ANDnXOR/ANDnXOR_DC26_Badge/Firmware/components/console_gfx.c

/*****************************************************************************
 * Made with beer and late nights in California.
 *
 * (C) Copyright 2017-2018 AND!XOR LLC (http://andnxor.com/).
 *
 * PROPRIETARY AND CONFIDENTIAL UNTIL AUGUST 7th, 2018 then,
 *
 * Licensed under the Apache License, Version 2.0 (the "License");
 * you may not use this file except in compliance with the License.
 * You may obtain a copy of the License at
 *
 *     http://www.apache.org/licenses/LICENSE-2.0
 *
 * Unless required by applicable law or agreed to in writing, software
 * distributed under the License is distributed on an "AS IS" BASIS,
 * WITHOUT WARRANTIES OR CONDITIONS OF ANY KIND, either express or implied.
 * See the License for the specific language governing permissions and
 * limitations under the License.
 *
 * ADDITIONALLY:
 * If you find this source code useful in anyway, use it in another electronic
 * conference badge, or just think it's neat. Consider buying us a beer
 * (or two) and/or a badge (or two). We are just as obsessed with collecting
 * badges as we are in making them.
 *
 * Contributors:
 *   @andnxor
 *   @zappbrandnxor
 *   @hyr0n1
 *   @exc3ls1or
 *   @lacosteaef
 *   @bitstr3m
 *****************************************************************************/

#include "system.h"

void console_gfx_area_banner(int i){
    switch(i){
		case 0 : util_print_nice(
				"\n"
				"           ██░ ██  ▒█████   ███▄ ▄███▓▓█████     ██▒   █▓ ██▓ ██▓     ██▓    ▄▄▄        ▄████ ▓█████ \n"
				"          ▓██░ ██▒▒██▒  ██▒▓██▒▀█▀ ██▒▓█   ▀    ▓██░   █▒▓██▒▓██▒    ▓██▒   ▒████▄     ██▒ ▀█▒▓█   ▀ \n"
				"          ▒██▀▀██░▒██░  ██▒▓██    ▓██░▒███       ▓██  █▒░▒██▒▒██░    ▒██░   ▒██  ▀█▄  ▒██░▄▄▄░▒███   \n"
				"          ░▓█ ░██ ▒██   ██░▒██    ▒██ ▒▓█  ▄      ▒██ █░░░██░▒██░    ▒██░   ░██▄▄▄▄██ ░▓█  ██▓▒▓█  ▄ \n"
				"          ░▓█▒░██▓░ ████▓▒░▒██▒   ░██▒░▒████▒      ▒▀█░  ░██░░██████▒░██████▒▓█   ▓██▒░▒▓███▀▒░▒████▒\n"
				"           ▒ ░░▒░▒░ ▒░▒░▒░ ░ ▒░   ░  ░░░ ▒░ ░      ░ ▐░  ░▓  ░ ▒░▓  ░░ ▒░▓  ░▒▒   ▓▒█░ ░▒   ▒ ░░ ▒░ ░\n"
				"           ▒ ░▒░ ░  ░ ▒ ▒░ ░  ░      ░ ░ ░  ░      ░ ░░   ▒ ░░ ░ ▒  ░░ ░ ▒  ░ ▒   ▒▒ ░  ░   ░  ░ ░  ░\n"
				"           ░  ░░ ░░ ░ ░ ▒  ░      ░      ░           ░░   ▒ ░  ░ ░     ░ ░    ░   ▒   ░ ░   ░    ░   \n"
				"           ░  ░  ░    ░ ░         ░      ░  ░         ░   ░      ░  ░    ░  ░     ░  ░      ░    ░  ░\n"
				"                                                     ░                                               \n"
				"\n"
				"                 ╡░                                                                             ╡░    \n"
				"                 ╡░        ╡░                                                        ╡░         ╡░    \n"
				"               ╡░╡░╡░      ╡░         ╡░                                  ╡░         ╡░       ╡░╡░╡░  \n"
				"               ╡░░░░░    ╡░╡░╡░       ╡░                                  ╡░       ╡░╡░╡░     ╡░░░░░  \n"
				"                 ╡░      ╡░░░░░     ╡░╡░╡░          ≈≈≈≈≈≈≈≈≈≈≈≈≈≈≈≈≈   ╡░╡░╡░     ╡░░░░░       ╡░    \n"
				"         ·*··∙.  ╡░        ╡░       ╡░░░░░         ≈≈≈≈≈≈≈≈≈≈≈≈≈≈≈≈≈    ╡░░░░░       ╡░         ╡░    \n"
				"         ······°·····∙·    ╡░         ╡░          ≈≈≈≈≈≈≈≈≈≈≈≈≈≈≈≈≈║      ╡░         ╡░     ··.·······\n"
				"         ▓▓▓▓▓·∙.··∙·.·········∙·     ╡░         ≈≈≈≈≈≈≈≈≈≈≈≈≈≈≈≈≈ ║      ╡░   ··°·.·∙····∙··▓▓▓▓▓▓▓▓▓\n"
				"         ▓▓▓▓▓▓▓▓▓▓▓▓▓··.·*···········╡░·····   ≈≈≈≈≈≈≈≈≈≈≈≈≈≈≈≈≈  ║  ····╡░*.···▓▓▓▓▓▓▓▓▓▓▓▓▓▓▓▓▓▓▓▓▓\n"
				"         ··▓▓▓▓▓▓▓▓▓▓▓▓▓▓▓▓▓▓▓▓▓▓▓·∙····*···∙····║·  ║         ║   ║·.··∙·······▓▓▓▓▓▓▓▓▓▓▓▓▓▓▓·······\n"
				"         ···········▓▓▓▓▓▓▓▓▓▓▓▓▓▓▓▓▓▓▓▓▓▓▓▓···∙·║···║·┌┐···.··║···║···▓▓▓▓▓▓▓▓▓▓▓▓▓▓▓···········∙··*·\n"
				"         ···°.···*···········▓▓▓▓▓▓▓▓▓▓▓▓▓▓▓▓▓▓▓▓║▓··║·││··◙···║·.·║▓▓▓▓▓▓▓▓▓▓▓▓▓▓▓▓▓▓····╡░··°·······\n"
				"         ·*··.∙°········∙∙∙·········.····▓▓▓▓▓▓▓▓║▓▓▓║▓││┌───┐▓║▓▓▓║▓▓▓▓▓▓·········∙······╡░····*·····\n"
				"         ··∙······.··╡░······∙∙·····∙··········▓▓║▓▓▓▓▓╘╛▓▓▓▓▓▓║▓▓▓▓▓······*···╡░···°···╡░╡░╡░·····.°·\n"
				"         ······∙·····╡░···*··.···╡░··.°·*·······▓║▓▓▓▓▓▓▓▓▓▓▓▓▓║▓▓····.∙·······╡░·······╡░░░░░····°···\n"
				"         ·∙··*···.·╡░╡░╡░···∙····╡░········.····▓║▓░δ▓▓▓▓▓▓▓▓▓▓║▓···°····.···╡░╡░╡░··*∙···╡░···.····∙·\n"
				"         ··········╡░░░░░······╡░╡░╡░···∙······▓▓║▓░░▓▓▓▓▓▓▓▓▓▓║▓▓···∙···∙···╡░░░░░·······╡░·∙···╡░···\n"
				"         °··╡░···°···╡░······*·╡░░░░░·········▓▓▓▓▓▓▓▓▓▓▓▓▓▓▓▓▓▓▓▓▓···*········╡░···°··∙··╡░·····╡░···\n"
				"         ·.·╡░··.····╡░·.·∙.·····╡░····∙°··▓▓▓▓▓▓··········∙····▓▓▓▓▓▓··°.··*··╡░·∙··.·∙·······╡░╡░╡░·\n"
				"         ·╡░╡░╡░·····╡░·····∙····╡░······▓▓▓▓▓▓▓·∙·τ·········∙···▓▓▓▓▓▓▓·······╡░···∙···*····.·╡░░░░░·\n"
				"         ·╡░░░░░··∙*·············╡░··▓▓▓▓▓▓▓▓▓·····☺≡≡≡⌐··..*······▓▓▓▓▓▓▓▓▓▓········°···········╡░···\n"
				"         ···╡░········∙·.····▓▓▓▓▓▓▓▓▓▓▓▓▓·····∙····╘·╘·······.·∙·······▓▓▓▓▓▓▓▓▓▓▓▓·············╡░···\n"
				"         ···╡░······°·····▓▓▓▓▓▓▓▓▓▓▓·°···∙······∙·······°······.·······.··▓▓▓▓▓▓▓▓▓▓▓▓··∙°··*···╡░···\n"
				"         ···╡░··▓▓▓▓▓▓▓▓▓▓▓▓▓·····∙···∙···∙··*···°·····∙·.··..··.··°··············▓▓▓▓▓▓▓▓▓▓▓▓▓·······\n"
				"         ▓▓▓▓▓▓▓▓▓▓▓▓▓▓▓▓▓·····°····*············∙····°·········.···*······..········▓▓▓▓▓▓▓▓▓▓▓▓▓▓▓▓▓\n"
				"\n");
				break;

    	case 1 : util_print_nice(
    			"\n"
    			"     ███▄    █  ▒█████   ██▀███  ▄▄▄█████▓ ██░ ██     ██▒   █▓ ██▓ ██▓     ██▓    ▄▄▄        ▄████ ▓█████ \n"
    			"     ██ ▀█   █ ▒██▒  ██▒▓██ ▒ ██▒▓  ██▒ ▓▒▓██░ ██▒   ▓██░   █▒▓██▒▓██▒    ▓██▒   ▒████▄     ██▒ ▀█▒▓█   ▀ \n"
    			"    ▓██  ▀█ ██▒▒██░  ██▒▓██ ░▄█ ▒▒ ▓██░ ▒░▒██▀▀██░    ▓██  █▒░▒██▒▒██░    ▒██░   ▒██  ▀█▄  ▒██░▄▄▄░▒███   \n"
    			"    ▓██▒  ▐▌██▒▒██   ██░▒██▀▀█▄  ░ ▓██▓ ░ ░▓█ ░██      ▒██ █░░░██░▒██░    ▒██░   ░██▄▄▄▄██ ░▓█  ██▓▒▓█  ▄ \n"
    			"    ▒██░   ▓██░░ ████▓▒░░██▓ ▒██▒  ▒██▒ ░ ░▓█▒░██▓      ▒▀█░  ░██░░██████▒░██████▒▓█   ▓██▒░▒▓███▀▒░▒████▒\n"
    			"    ░ ▒░   ▒ ▒ ░ ▒░▒░▒░ ░ ▒▓ ░▒▓░  ▒ ░░    ▒ ░░▒░▒      ░ ▐░  ░▓  ░ ▒░▓  ░░ ▒░▓  ░▒▒   ▓▒█░ ░▒   ▒ ░░ ▒░ ░\n"
    			"    ░ ░░   ░ ▒░  ░ ▒ ▒░   ░▒ ░ ▒░    ░     ▒ ░▒░ ░      ░ ░░   ▒ ░░ ░ ▒  ░░ ░ ▒  ░ ▒   ▒▒ ░  ░   ░  ░ ░  ░\n"
    			"       ░   ░ ░ ░ ░ ░ ▒    ░░   ░   ░       ░  ░░ ░        ░░   ▒ ░  ░ ░     ░ ░    ░   ▒   ░ ░   ░    ░   \n"
    			"             ░     ░ ░     ░               ░  ░  ░         ░   ░      ░  ░    ░  ░     ░  ░      ░    ░  ░\n"
    			"                                                          ░                                               \n"
				"\n"
				"     ▲▲▲▲▲▲▲▲▲▲▲▲▲▲▲▲▲▲▲▲▲▲▲▲▲▲▲▲▲▲▲▲▲▲▲▲▲▲▲▲▲▲▲▲▲▲▲▲▲▲▲▲▲▲▲▲▲▲▲▲▲▲▲▲▲▲▲▲▲▲▲▲▲▲▲▲▲▲▲▲▲▲▲▲▲▲▲▲▲▲▲▲▲▲▲▲▲▲▲▲\n"
    			"     ════════════════════════════════════════════════════════════════════════════════════════════════════\n"
				"     ████████████████████████████████████████████████████████████████████████████████████████████████████\n"
				"     ░░░░░░░░░░░░░░░░░░░░░░░░░░░░░░░░░░░░░░░░░░░░░░░░░░░░░░░░░░░░░░░░░░░░░░░░░░░░░░░░░░░░░░░░░░░░░░░░░░░░\n"
				"     ░░░░░░░░░░░░░░░░░░░░░░░░░░░░░░░░░░░░░░░░░░░░░░░░░░░░░░░░░░░░░░░░░░░░░░░░░░░░░░░░░░░░░░░░░░░░░░░░░░░░\n"
				"     ░░░░░░░░░░░░░░░░░░░░░░░░░░░░░░░░░░░░░░░░░░░░░░░░░░░░░░░░░░░░░░░░░░░░░░░░░░░░░░░░░░░░░░░░░░░░░░░░░░░░\n"
				"     ░░░░░░░░░▒▒▒▒▒░░░░░░░░░░░░░░░░░░░░░░░░░░░░░░░░░░░░░░░░░░░░░░░░░┌─────────────┐░░░░░░░░░░░░░░░░░░░░░░\n"
				"     ░░░░░░░░▒     ▒░░░░░░░░░░░░░░░░░░░░░░░░░░░╔═══════╦═══════╗░░░░│ COMDEX TIX! │░░░░░░«≈≈≈≈≈≈≈≈≈»░░░░░\n"
				"     ░░░░░░░▒       ▒░░░░░░░┌─────────────┐░░░░║       ║       ║░░░░│             │░░░░░░« WANTED! »░░░░░\n"
				"     ░░░░░░▒ ░░░░    ▒░░░░░░││Lead Solder││░░░░║       ║       ║░░░░│PREORDER NOW!│░░░░░░«    •    »░░░░░\n"
				"     ░░░░░▒  ░   ░    ▒░░░░░││ Only 0.25 ││░░░░║       ║       ║░░░░│             │░░░░░░«    │    »░░░░░\n"
				"     ░░░░░▒  ░   ░    ▒░░░░░│             │░░░░║       ║       ║░░░░│ COMES  WITH │░░░░░░«   ░░░   »░░░░░\n"
				"     ░░░░░▒  ░░░░     ▒░░░░░│TRS-80 POCKET│░░░░║       ║       ║░░░░│  CARDSTOCK  │░░░░░░«  (○░○)  »░░░░░\n"
				"     ░░░░░▒  ░  ░     ▒░░░░░│ WITH BASIC! │░░░░║       ║       ║░░░░│    BADGE!   │░░░░░░«   ░░░   »░░░░░\n"
				"     ░░░░░▒  ░  ░░    ▒░░░░░│             │░░░░║      █║█      ║░░░░│             │░░░░░░«   ╪╪╪   »░░░░░\n"
				"     ░░░░░░▒ ░   ░░  ▒░░░░░░│HAM RADIO KIT│░░░░║      █║█      ║░░░░├☻ ☻ ☻ ☻ ☻ ☻ ☻┤░░░░░░«   ░░░   »░░░░░\n"
				"     ░░░░░░░▒       ▒░░░░░░░│  WTF $40!!  │░░░░║      █║█      ║░░░░│             │░░░░░░«    ║    »░░░░░\n"
				"     ░░░░░░░░▒     ▒░░░░░░░░└─────────────┘░░░░║      █║█      ║░░░░│CARDIFF GIANT│░░░░░░« REWARD! »░░░░░\n"
				"     ░░░░░░░░░▒▒▒▒▒░░░░░░░░░░░░░░░░░░░░░░░░░░░░║      █║█      ║░░░░│  √PC $1337  │░░░░░░«≈≈≈≈≈≈≈≈≈»░░░░░\n"
				"     ░░░░░░░░░░░░░░░░░░░░░░░░░░░░░░░░░░░░░░░░░░║       ║       ║░░░░└─────────────┘░░░░░░░░░░░░░░░░░░░░░░\n"
				"     ░░░░░░░░░░░░░░░░░░░░░░░░░░░░░░░░░░░░░░░░░░║       ║       ║░░░░░░░░░░░░░░░░░░░░░░░░░░░░░░░░░░░░░░░░░\n"
				"     ░░░░░░░░░░░░░░░░░░░░░░░░░░░░░░░░░░░░░░░░░░║       ║       ║░░░░░░░░░░░░░░░░░░░░░░░░░░░░░░░░░░░░░░░░░\n"
				"     ░░░░░░░░░░░░░░░░░░░░░░░░░░░░░░░░░░░░░░░░░░║       ║       ║░░░░░░░░░░░░░░░░░░░░░░░░░░░░░░░░░░░░░░░░░\n"
				"     ████████████████████████████████████████████████████████████████████████████████████████████████████\n"
				"\n");
    			break;

    	case 2 : util_print_nice(
    			"\n"
    			"      ██████  ▒█████   █    ██ ▄▄▄█████▓ ██░ ██     ██▒   █▓ ██▓ ██▓     ██▓    ▄▄▄        ▄████ ▓█████ \n"
    			"    ▒██    ▒ ▒██▒  ██▒ ██  ▓██▒▓  ██▒ ▓▒▓██░ ██▒   ▓██░   █▒▓██▒▓██▒    ▓██▒   ▒████▄     ██▒ ▀█▒▓█   ▀ \n"
    			"    ░ ▓██▄   ▒██░  ██▒▓██  ▒██░▒ ▓██░ ▒░▒██▀▀██░    ▓██  █▒░▒██▒▒██░    ▒██░   ▒██  ▀█▄  ▒██░▄▄▄░▒███   \n"
    			"      ▒   ██▒▒██   ██░▓▓█  ░██░░ ▓██▓ ░ ░▓█ ░██      ▒██ █░░░██░▒██░    ▒██░   ░██▄▄▄▄██ ░▓█  ██▓▒▓█  ▄ \n"
    			"    ▒██████▒▒░ ████▓▒░▒▒█████▓   ▒██▒ ░ ░▓█▒░██▓      ▒▀█░  ░██░░██████▒░██████▒▓█   ▓██▒░▒▓███▀▒░▒████▒\n"
    			"    ▒ ▒▓▒ ▒ ░░ ▒░▒░▒░ ░▒▓▒ ▒ ▒   ▒ ░░    ▒ ░░▒░▒      ░ ▐░  ░▓  ░ ▒░▓  ░░ ▒░▓  ░▒▒   ▓▒█░ ░▒   ▒ ░░ ▒░ ░\n"
    			"    ░ ░▒  ░ ░  ░ ▒ ▒░ ░░▒░ ░ ░     ░     ▒ ░▒░ ░      ░ ░░   ▒ ░░ ░ ▒  ░░ ░ ▒  ░ ▒   ▒▒ ░  ░   ░  ░ ░  ░\n"
    			"    ░  ░  ░  ░ ░ ░ ▒   ░░░ ░ ░   ░       ░  ░░ ░        ░░   ▒ ░  ░ ░     ░ ░    ░   ▒   ░ ░   ░    ░   \n"
    			"          ░      ░ ░     ░               ░  ░  ░         ░   ░      ░  ░    ░  ░     ░  ░      ░    ░  ░\n"
    			"                                                        ░                                               \n"
				"\n"
    			"                               ██████████████████░░░░░░░░░░░░░░░░░░░░░░▒█                              \n"
    			"               █▒                ▓▒              ░▓                      ▒█                            \n"
    			"                 ██░               ▒▓              ▓▓                      ▒█                          \n"
    			"                   ██▓▓▓▓▓▒▒▒▒▒▒░░░░░▒███████▓▓▓▓▓▓▓▓████████████████████████████                      \n"
    			"      ██  ███████████████████████████████████                                           ██             \n"
    			"      █████████████████████████████████████           ██   ██████████████  █████████████ █             \n"
    			"    ████████████████████████████████████ █  ███████  █ ██  ████   ████████  █    █████████             \n"
    			"      ██▓▒▒▒▒▒▒▒▒▓▓▓▓▓▓▓▓▓▓▓▓▓▓███████░█ ██    ████  ██ █   █████     ████  ████      █████            \n"
    			"      █ ▒                              █ ████ █   █  ████   ███████          ███████      ██           \n"
    			"      █ ▒                              █ ████████     █   █  ████████         ██████ ██   ████         \n"
    			"        ▒                              █              █  ██  █████████    ██   ████████████ ██         \n"
    			"        ░                              █           ██ █████     █████████                    ██        \n"
    			"     █  ░                              █           █                                         █████     \n"
    			"     █  ░                              █                                                           ██  \n"
    			"     █ █░                              █                                      █████████████████████    \n"
    			"     █ █▓▒▒░░░░                        █                                  █████████████     ███████ ██ \n"
    			"     █                      ████████████                                █████ ██ ████████████  ███████ \n"
    			"     █       ████████                            █  ████████     ██     ███      █████████████  ███ ██ \n"
    			"     █      ██████ ████                         █ ████████████          ██ █     ████████████     █  █ \n"
    			"      ██████ ██ ███ ████                       █ ███████   █████                 ████████████         █\n"
    			"             ██  ███ ███████                   ██████ █ █  ██ ██████       █████            █████████ █\n"
    			"              ███    █████             ██████████████ ██  █  ████████   ████████████████████████       \n"
    			"                ████████        ██████████████████████ ███  █ ███████         ████████████████         \n"
    			"                            █████████████████████████████ ██████████████████████████████████           \n"
    			"                                               ████████████████████████████████████████████████        \n"
				"\n");
    			break;

    	case 3 : util_print_nice(
    			"\n"
    			"         ▓█████ ▄▄▄        ██████ ▄▄▄█████▓    ██▒   █▓ ██▓ ██▓     ██▓    ▄▄▄        ▄████ ▓█████ \n"
    			"         ▓█   ▀▒████▄    ▒██    ▒ ▓  ██▒ ▓▒   ▓██░   █▒▓██▒▓██▒    ▓██▒   ▒████▄     ██▒ ▀█▒▓█   ▀ \n"
    			"         ▒███  ▒██  ▀█▄  ░ ▓██▄   ▒ ▓██░ ▒░    ▓██  █▒░▒██▒▒██░    ▒██░   ▒██  ▀█▄  ▒██░▄▄▄░▒███   \n"
    			"         ▒▓█  ▄░██▄▄▄▄██   ▒   ██▒░ ▓██▓ ░      ▒██ █░░░██░▒██░    ▒██░   ░██▄▄▄▄██ ░▓█  ██▓▒▓█  ▄ \n"
    			"         ░▒████▒▓█   ▓██▒▒██████▒▒  ▒██▒ ░       ▒▀█░  ░██░░██████▒░██████▒▓█   ▓██▒░▒▓███▀▒░▒████▒\n"
    			"         ░░ ▒░ ░▒▒   ▓▒█░▒ ▒▓▒ ▒ ░  ▒ ░░         ░ ▐░  ░▓  ░ ▒░▓  ░░ ▒░▓  ░▒▒   ▓▒█░ ░▒   ▒ ░░ ▒░ ░\n"
    			"          ░ ░  ░ ▒   ▒▒ ░░ ░▒  ░ ░    ░          ░ ░░   ▒ ░░ ░ ▒  ░░ ░ ▒  ░ ▒   ▒▒ ░  ░   ░  ░ ░  ░\n"
    			"            ░    ░   ▒   ░  ░  ░    ░              ░░   ▒ ░  ░ ░     ░ ░    ░   ▒   ░ ░   ░    ░   \n"
    			"            ░  ░     ░  ░      ░                    ░   ░      ░  ░    ░  ░     ░  ░      ░    ░  ░\n"
    			"                                                   ░                                               \n"
    			"\n"
    			"                                                     █████                           \n"
    			"                           ≡≡≡   ≡≡                ████████              ≡≡≡   ≡≡   \n"
    			"                          ≡≡≡≡≡ ≡≡≡≡              █████████             ≡≡≡≡≡ ≡≡≡≡   \n"
    			"                          ≡≡≡░≡  ≡░≡              ██████████            ≡≡≡░≡  ≡░≡   \n"
    			"                     ≡≡≡≡   ░░ ░░░    ≡≡         ████████████      ≡≡≡≡   ░░ ░░░    ≡≡  \n"
    			"                    ≡≡≡░░   ░░ ░░░   ≡≡≡║       █████████████     ≡≡≡░░   ░░ ░░░   ≡≡≡║ \n"
    			"                    ≡≡░░░░░ ░░ ░░    ░≡≡≡      ███████████████    ≡≡░░░░░ ░░ ░░    ░≡≡≡    \n"
    			"                     ≡≡░░░░ ░░░░░    ░░        ███████████████     ≡≡░░░░ ░░░░░    ░░              \n"
    			"                         ░░  ░░░    ░░        █████████████████        ░░  ░░░    ░░        	   \n"
    			"                         ░░░  ░░    ░░        █████████████████        ░░░  ░░    ░░         	   \n"
    			"                     ≡≡≡   ░░░░░    ░░        █████████████████    ≡≡≡   ░░░░░    ░░               \n"
    			"               ≡    ≡≡░≡   ░░░░░   ░░░ ≡≡    ███████████████████  ≡≡░≡   ░░░░░   ░░░ ≡≡     ≡      \n"
    			"              ≡▓≡    ≡≡░░    ░░░   ░░░░≡≡≡  █████████████████████   ≡≡░░    ░░░   ░░░░≡≡≡   ≡▓≡     \n"
    			"             ≡▒▓▓≡     ░░░   ░░░  ░░░░░≡≡   █████████████████████     ░░░   ░░░  ░░░░░≡≡   ≡▒▓▓≡    \n"
    			"             ≡▒▓▓≡       ░░░  ░░ ░░░░░      █████████████████████       ░░░  ░░ ░░░░░      ≡▒▓▓≡    \n"
    			"         ≡≡  ≡▒▓▓≡  ≡≡   ░░░  ░░ ░░░       █████████      ████████      ░░░  ░░ ░░░    ≡≡  ≡▒▓▓≡  ≡≡\n"
    			"        ≡▓▓≡ ≡▒▓▓≡ ≡▓▓≡    ░░░░░░░░        ████████        ███████        ░░░░░░░░    ≡▓▓≡ ≡▒▓▓≡ ≡▓▓≡\n"
    			"        ≡▓▓≡≡≡▓▓▓≡≡≡▓▓≡    ░░░░░░░         ███████          ██████        ░░░░░░░     ≡▓▓≡≡≡▓▓▓≡≡≡▓▓≡\n"
    			"        ≡▓▓▓▓▓▓▓▓▓▓▓▓▓≡     ░░░░░          ██████           ██████         ░░░░░      ≡▓▓▓▓▓▓▓▓▓▓▓▓▓≡\n"
    			"         ≡▓▓▓▓▓▓▓▓▓▓▓≡      ░░░░          ███████            ██████        ░░░░        ≡▓▓▓▓▓▓▓▓▓▓▓≡\n"
    			"          ≡≡≡≡▒▓▓≡≡≡≡        ░░░          ██████              ██████        ░░░         ≡≡≡≡▒▓▓≡≡≡≡ \n"
    			"             ≡▒▓▓≡           ░░░          ██████              ██████        ░░░            ≡▒▓▓≡    \n"
    			"             ≡▒▓▓≡           ░░░         ███████              ███████       ░░░            ≡▒▓▓≡    \n"
    			"             ≡▒▓▓≡           ░░░         ██████                ██████       ░░░            ≡▒▓▓≡    \n"
				"\n");
    			break;

    	case 4 : util_print_nice(
    			"\n"
    			"          █     █░▓█████   ██████ ▄▄▄█████▓    ██▒   █▓ ██▓ ██▓     ██▓    ▄▄▄        ▄████ ▓█████ \n"
    			"         ▓█░ █ ░█░▓█   ▀ ▒██    ▒ ▓  ██▒ ▓▒   ▓██░   █▒▓██▒▓██▒    ▓██▒   ▒████▄     ██▒ ▀█▒▓█   ▀ \n"
    			"         ▒█░ █ ░█ ▒███   ░ ▓██▄   ▒ ▓██░ ▒░    ▓██  █▒░▒██▒▒██░    ▒██░   ▒██  ▀█▄  ▒██░▄▄▄░▒███   \n"
    			"         ░█░ █ ░█ ▒▓█  ▄   ▒   ██▒░ ▓██▓ ░      ▒██ █░░░██░▒██░    ▒██░   ░██▄▄▄▄██ ░▓█  ██▓▒▓█  ▄ \n"
    			"         ░░██▒██▓ ░▒████▒▒██████▒▒  ▒██▒ ░       ▒▀█░  ░██░░██████▒░██████▒▓█   ▓██▒░▒▓███▀▒░▒████▒\n"
    			"         ░ ▓░▒ ▒  ░░ ▒░ ░▒ ▒▓▒ ▒ ░  ▒ ░░         ░ ▐░  ░▓  ░ ▒░▓  ░░ ▒░▓  ░▒▒   ▓▒█░ ░▒   ▒ ░░ ▒░ ░\n"
    			"           ▒ ░ ░   ░ ░  ░░ ░▒  ░ ░    ░          ░ ░░   ▒ ░░ ░ ▒  ░░ ░ ▒  ░ ▒   ▒▒ ░  ░   ░  ░ ░  ░\n"
    			"           ░   ░     ░   ░  ░  ░    ░              ░░   ▒ ░  ░ ░     ░ ░    ░   ▒   ░ ░   ░    ░   \n"
    			"             ░       ░  ░      ░                    ░   ░      ░  ░    ░  ░     ░  ░      ░    ░  ░\n"
				"\n"
    			"                                        ▒▒▒▒▒▒▒▒▒▒▒▒▒▒▒▒▒▒▒▒▒▒▒▒▒▒▒\n"
    			"                                         ▒░░░░░░░░░░░░░░░░░░░░░░░▒\n"
    			"                                          ▒                     ▒\n"
    			"                                          ▒  ☼   B 0 0 Z 3   ☼  ▒\n"
    			"                                         ░▒                     ▒░\n"
    			"                                        ░░▒░░░░░░░░░░░░░░░░░░░░░▒░░\n"
    			"                                  ▒▒▒▒▒▒▒▒▒▒▒▒▒▒▒▒▒▒▒▒▒▒▒▒▒▒▒▒▒▒▒▒▒▒▒▒▒▒▒\n"
    			"                                   ▒▒║║║║│║║▒░░░░░░░░░░░░░░░░░▒║║║○║║║▒▒\n"
    			"        ▒▒▒▒▒▒▒▒▒▒▒▒▒▒▒▒▒▒▒▒▒▒▒▒▒▒▒▒▒║║║║│║║▒░░             ░░▒║║│║║║║▒▒▒▒▒▒▒▒▒▒▒▒▒▒▒▒▒▒▒▒▒▒▒▒▒▒▒▒▒\n"
    			"        ░░░░░░░░░░░░░░░░░░░░░░░░░░░░▒║║║║║│║▒░               ░▒│║│║║║║▒░░░░░░░░░░░░░░░░░░░░░░░░░░░░\n"
    			"        ▒▒▒▒▒▒▒▒▒▒▒▒▒▒▒▒▒▒▒▒▒▒▒▒▒▒▒▒▒│║│║║│║▒                 ▒│║│║║║║▒▒▒▒▒▒▒▒▒▒▒▒▒▒▒▒▒▒▒▒▒▒▒▒▒▒▒▒▒\n"
    			"                                  ░░▒║││○║│║▒     ╔═╗ ╔═╗     ▒│║│║║│║▒░░\n"
    			"           ░░░░░░       ░░░░░░     ░▒║││║║│║▒    ╔╝♠║ ║♠╚╗    ▒║║│║║│║▒░     ░░░░░░       ░░░░░░\n"
    			"           ║║║║║║       ║║║║║║      ▒○║│║║│║▒   ╔╝──║ ║──╚╗   ▒║║│║║│║▒      ║║║║║║       ║║║║║║\n"
    			"          ░░░░░░░░     ░░░░░░░░     ▒║║│║║│║▒  ╔╝───║ ║───╚╗  ▒║║║║│║║▒     ░░░░░░░░     ░░░░░░░░\n"
    			"          ║║║║║║║║     ║║║║║║║║     ▒║║│║║║║▒Θ╔╣────║ ║────╠╗Θ▒║║║║│║║▒     ║║║║║║║║     ║║║║║║║║\n"
    			"         ░░░░░░░░░░   ░░░░░░░░░░    ▒║║║║║║║▒Θ╠╝────║ ║────╚╣Θ▒║║║║│○│▒    ░░░░░░░░░░   ░░░░░░░░░░\n"
    			"         ║║║║║║║║║║   ║║║║║║║║║║    ▒║║║║║║│▒ ║♦────║ ║────♦║ ▒║○║║║║│▒    ║║║║║║║║║║   ║║║║║║║║║║\n"
    			"         ║║║XXXX║║║   ║║║XXXX║║║    ▒│║║║│║│▒ ║─────║ ║─────║ ▒║║║│║║│▒    ║║║XXXX║║║   ║║║XXXX║║║\n"
    			"         ║║║║║║║║║║   ║║║║║║║║║║    ▒│║○║│║│▒ ║─────║ ║─────║ ▒║║║│║║│▒    ║║║║║║║║║║   ║║║║║║║║║║\n"
    			"         ░░░░░░░░░░   ░░░░░░░░░░    ▒│║║║│║│▒ ║♥───♣║ ║♣───♥║ ▒║║║│║║║▒    ░░░░░░░░░░   ░░░░░░░░░░\n"
    			"          ║║║║║║║║     ║║║║║║║║     ▒│║║║║║║▒Θ╠╗───╔╣ ╠╗───╔╣Θ▒║║║│║║║▒     ║║║║║║║║     ║║║║║║║║\n"
    			"          ░░░░░░░░     ░░░░░░░░     ▒║║║│║║║▒Θ╚╩═══╩╝ ╚╩═══╩╝Θ▒║║○║║│║▒     ░░░░░░░░     ░░░░░░░░\n"
    			"           ║║║║║║       ║║║║║║     ░▒║║║│║║║▒                 ▒│║║║║║║▒░     ║║║║║║       ║║║║║║\n"
    			"           ░░░░░░       ░░░░░░    ░░▒║║║║║║║▒                 ▒│║║║║║║▒░░    ░░░░░░       ░░░░░░\n"
				"        ▒▒▒▒▒▒▒▒▒▒▒▒▒▒▒▒▒▒▒▒▒▒▒▒▒▒▒▒▒▒▒▒▒▒▒▒▒▒▒▒▒▒▒▒▒▒▒▒▒▒▒▒▒▒▒▒▒▒▒▒▒▒▒▒▒▒▒▒▒▒▒▒▒▒▒▒▒▒▒▒▒▒▒▒▒▒▒▒▒▒▒▒\n"
				"\n");
    			break;
    }
}

void console_gfx_area_eggz(int i){
    switch(i){
		case 0 : util_print_nice(//HOME VILLAGE
				"\n"
				"                                     ░██████ ░██░                              \n"
				"                              ▒█░       ▒▒▒▓        █▓                         \n"
				"                         ▒██            ▓▒▒▓      ░  ░ █                       \n"
				"                       █          ░░░░███████▒░▒░██░    ░                      \n"
				"                     █            ░█▒▒▒▒▒▒▒▒▓▓▓█░ ░▒██▓  ░░                    \n"
				"                    █       █████▒░█▒▒▒▓▒▓▒█▓▓▓█░        ▓██                   \n"
				"                   ░      ██░     ░█▓▒████▓▓▓▓▓█░  ▓█░      █░                 \n"
				"                  ▒█ ▓█           ░█▓▒▓▓▓█▓▓▓▓▓█░       █░    █                \n"
				"                 ██░              ░█▓▓▓▓▓▓▓▓▓▓▓█░          ░█                  \n"
				"                 █▓░        ▓█▓░  ░░████████████░█████▒      ██                \n"
				"                ░░  ▒░ ▓▓        ░████▓███████░░░        ░██  ░                \n"
				"                ▒█░░█    ▒██░ ░██  ░░▓▓▓▓▓▓█▓░░░░    ▒█▒░░   █░█               \n"
				"               ███                                              █              \n"
				"             ▓█░  ░▒███▒░                  ░░░░▒▒▒▒▒▒░░         ░▒██░          \n"
				"   ████░░           ░▓████████████████████████▒░        ▓████▓███████████      \n"
				"  █ ░▓▓██████████████████▒          ███████████▒        █████░██████████████   \n"
				"  ▒███████████████▓█████░░       ░██▒          ░▓█▒█▓█████████████████████████ \n"
				"  ▓███████████████▓█████░██▓░ ▒██████▒░  ░██░█████▒      ██ ███▓███▒██████████▒\n"
				"  ▓██████░██░ ░████████░██ █ █▒▓ ████████████▒████ █████░██▒███████████████████\n"
				"   ██████████▓████▓███░ ▓████████████░█░██ ▓▓█████████████░██████████░████████ \n"
				"    ░██████░███████▓░██░█████▓▓░██████░░███░█▓████░▒▒█████░███████████▓█████▓  \n"
				"       ███▓▓███░███████░█████  ░█████▓█████▓ █▒▒██░  █████ ██████████████▓░    \n"
				"           █░███░█░████░████████████▒██ ████▒█ █░▓███████  █████▒█████▓        \n"
				"                  █▓███  ██████████ ▓█░██████ █▓░▓▒░██▓ ░████▒██▓              \n"
				"                   █▓█░ █░  ░░░   █░▒▒▒▒▒▒▒▒▒░░░█▓▓██   ░█████                 \n"
				"                    ░█░░       ░█▓█████████████████████████▒                   \n"
				"                         ▒█████░                        ░▓              ▓███   \n"
				"                         ░█                             ░█      ▒███░   ▒▒██   \n"
				"                          █  ███ ▒▓▒█ ▒▒ █░▓▒ █▒▓▒░▒▒██ ▒████░   ░  ░██░       \n"
				"                          █ █▒▒██▒▒▒█ ▒▒ █░▒▒ █▒▒▒██▒   ▓ ▒█  ▒██░             \n"
				"                          █░█░░█░▓█▒█ ▓▓ █░▓▓ █▒█▒█ ▓▒▓ ░██▒                   \n"
				"                          █ ▓███▒▒▒▒█ ▒▒ █░▒▒░█▓███████░░█                     \n"
				"                          █░░▒▓█ █▓▒█ ▓▓ █░▓█ █▒█▓░▓██░ ░█                     \n"
				"                          █▒     ░████████████████░     ░█                     \n"
				"                          ██                            ░█                     \n"
				"                             ░▒█████████████████████▓▒░                        \n"
				"\n");
				break;

		case 1 : util_print_nice(//NORTH VILLAGE
				"\n"
				"          ░░░░░░░░░░░░░░░░░░░░░░░░░░░░░░░░░▓▓▒▒▓░░▓░░░░░░░░░░░░░░░░░░░░░░░░░░░░░░░░░░░░░░\n"
				"          ░░░░░░░░░░░░░░░░░░░░░░░░░░░░░░░░█▓▓▓▓░░░▒▓▒▒░░░░░░░░░░░░░░░░░░░░░░░░░░░░░░░░░░░\n"
				"          ░░░░░░░░░░░░░░░░░░░░░░░░░░░█████▓▓▓▒▓▓▒▒▒▒▓▒░░░░░░░░░░░░░░░░░░░░░░░░░░░░░░░░░░░\n"
				"          ░░░░░░░░░░░░░░░░░░░░░▓▓▒██████▓▒█▓▒▓▓▒▓▓▒░▓▓▒▓▒▒▒▒▒▓▒░░█▓▓░░░░░░░░░░░░░░░░░░░░░\n"
				"          ░░░░░░░░░░░░░░░░░░░░▓▓▓▒▒█████▓██▓▓█▒▒▓▓▒░▓▒▒▓▒░▓▓▒▒▒▒█████░░░░░░░░░░░░░░░░░░░░\n"
				"          ░░░░░░░░░░░░░░░░░░░█▓▒▒▒▒▓█████▒█▓▓█▓▓▓▓▒▓▓█▒▓▒█▓▓▒▓▓█▓▓▓█▒▒░░░░░░░░░░░░░░░░░░░\n"
				"          ░░░░░░░░░░░░░░░░░▓███▒▒▒▒▒██████████▓▓▓▓▓▓▓▒▒▒▓████▒██▓▓▓▓▓▓░░░░░░░░░░░░░░░░░░░\n"
				"          ░░░░░░░░░░░░░░░░▓█████▓▒▓████▓▓██▒██▓▓▓▓▓▓▓▒▓█▓▓▓█░██████▓▓▓▓▓░░░░░░░░░░░░░░░░░\n"
				"          ░░░░░░░░░░░░░░░░██████████▒▓▓▓▓██▓▒█▓▓▓▓▓▓▓▓▒▓█▓▓▓░░░██▒█▓▓▓▓▓▒░░░░░░░░░░░░░░░░\n"
				"          ░░░░░░░░░░░░░░░██████████▓▓▓▓▓▓████▓▓▓▓▓▓▓▓░▒██▓▓▓▒▒░░█▓██▒▓▓▓▓▓░░░░░░░░░░░░░░░\n"
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
				"                ░░░░░░░░░░░░░░░░░░▓██████▓▓▒▒▒▓▓▓▒▓██▓▒▓▒▒▒▓▓▓▓▓▓▓▓▓▓████▓▓▓▓▓▓█▓████████▓░░░░░\n"
				"                ░░░░░░░░░░░░░░░░░▒▓██████▓▓▓▒▒▒▒▒▒▒▓▓▓▓▓▒▒▓▓▓▓▓▓▓▓▓▓▓█████▓▓▓▒▓▓█████████▓░░░░░\n"
				"                ░░░░░░░░░░░░░░░░░▒▓▓▓██▓██▓▓▒▒▒░▒▒▒▒▓▓▓▒▒▒▓██▓▓▓▓▓▓▓▓▓███▓▓▒▓██▓▓███████▓▒░░░░░\n"
				"                ░░░░░░░░░░░░▓▓░░░▓████▓░▓▓▓▓▓▓█▓▓▒▒▒▒▒▒▒▒█▓▓▓▓▓▓▓▓▓▓▒▓▓▓▓▓▓▓█▓▓▓▓▓██████▓▒░░░░░\n"
				"                ░░░░░░░░░░░▓▓▓░▓▓▓█▓▓▓▓░███▓█▓▓▒███▓▓▓▓▓▓██▓▓▓▓▓▓▓▓▓█▓▓▓▓█▓██▓▓▓▓▒████▓█▓▒░░░░░\n"
				"                ░░░░░░░░░░░▓▓▓▒▓▒▒▒▓▓█▓▒▒▓▓▓▓▓▓▓███▓▒▒▒▓▓▒▒▒▓▓▓▓▓██▓▒▒▓██▓██▓██▓▓▓▓███▒█▒▒░░░░░\n"
				"                ░░░░░░░░░▒▓▒▓▓▓▓▒▓▒▓▓▒▒▓▒▓▓▒▓▒▓█▓▓█▓▒▓▒▓▓▒▓▓▒▓▓▓▓▓▓▓▓▓▒▓▓▒▓▓▓█▓▒▓▓▒██▓▒▓▓▒░░▒░░\n"
				"                ░░░░░░░░░░▓▓▓▒▒▓▒▒▓██▒▒▒▓▓█▒▓▒▓▒▒▒▒▓▒▒▓▓▓▒▓▓▓▓▓▒▒▒▓▓▒▓█▓▓▒▓▓██▓▒▒▓▓▓█▓▒▒▒▓▒░▒▒░\n"
				"                ░░░░░░░░░░▓▒▓██▓▒▒▓██▓▓█▓▓█▓▒▓▓▓▒▓▒▓▒▒▓▓▓▒▓▓▓▓▓▓▓▒▓▓▓▒▓▓▓▒▒▒█▓▓▓▓▓▓▓▓▓▓▒░░░▒▒▒▒\n"
				"                ░░░░░░░░▒▓▓▓███▓▓▓▒▓██▓▓▓██▓▓███▓▓▓▓▓▓▒▓▓▓▓▓▓▓▓▓▓▒▓▓▓▓▒▓▓▓█▓▓██▓▓▓▓▒░▓▓░░░░░▒▒▒\n"
				"                ░░░░░░▒███████████▓▓████████▓██████▓▓▓▓▓▓▓▒▓▓▓▓▓▓████▓▓▓▓▓▒▒▓██▓▓█▓▒░▓▒░░░░░▒▒▒\n"
				"\n");
				break;
    }
}

void console_gfx_game_over(){
	util_print_nice(
			"  ███████ YOU ARE DEAD ██████\n"
			"  ███████████████████████████\n"
			"  ███████▀▀▀░░░░░░░▀▀▀███████\n"
			"  ████▀░░░░░░░░░░░░░░░░░▀████\n"
			"  ███│░░░░░░░░░░░░░░░░░░░│███\n"
			"  ██▌│░░░░░░░░░░░░░░░░░░░│▐██\n"
			"  ██░└┐░░░░░░░░░░░░░░░░░┌┘░██\n"
			"  ██░░└┐░░░░░░░░░░░░░░░┌┘░░██\n"
			"  ██░░┌┘▄▄▄▄▄░░░░░▄▄▄▄▄└┐░░██\n"
			"  ██▌░│██████▌░░░▐██████│░▐██\n"
			"  ███░│▐███▀▀░░▄░░▀▀███▌│░███\n"
			"  ██▀─┘░░░░░░░▐█▌░░░░░░░└─▀██\n"
			"  ██▄░░░▄▄▄▓░░▀█▀░░▓▄▄▄░░░▄██\n"
			"  ████▄─┘██▌░░░░░░░▐██└─▄████\n"
			"  █████░░▐█─┬┬┬┬┬┬┬─█▌░░█████\n"
			"  ████▌░░░▀┬┼┼┼┼┼┼┼┬▀░░░▐████\n"
			"  █████▄░░░└┴┴┴┴┴┴┴┘░░░▄█████\n"
			"  ███████▄░░░░░░░░░░░▄███████\n"
			"  ██████████▄▄▄▄▄▄▄██████████\n"
			"  ████████ GAME OVER ████████\n"
			"\n\n");
}

void console_gfx_game_over_alcohol_poisoning(){
	util_print_nice(
		"      ░▒░░░░░▒▒░░░░░░░░░░░░░▒░░░░░░░░░▓▓▓▓▓▓▓▓▓▓▓▓▓▓▓▓▓▓▓▓▓▓▓▓▓▓▓▓▒▒▒▒▓▓▓▓▓▓▓▓▓▓▓▓▓▓▓▓▓▓▓▓▓▓▓███████████▓\n"
		"      ░░░░▓▓▓▓▓░░░░▒░░░░░░░░░░░░░▒░░░▓▓▓▓▓▓▓▓▓▓▓▓▓▓▓▓▓▓▓▓▒▒▒▒▒▒▒▓▒▒▒▒▒▒▓▓▓▒▒▒▓▓▓▓▓▓▓▓▓▓▓▓▓█▓███████▓▓▓▓██\n"
		"      ░░░░▓▓▓▓▒░░░░░░░░░░░░░░░░░░▒▒░▓▓▓▓▓▓▓▓▓▓▓▓▓▓▓▓▒▒▒▒▒▓▓▓▒▒▒▒▒▒▒▒▓▓▓▓▓▓▓▓█▓▒▒▓░▒▒▒▓▓▓▓███████▓▓▓██▓█▓▓\n"
		"      ░░░░░░░░░░░░░░░░░░░░░░░░░░░░░▓▓▓▓▓▓▓▓▓▓▓▓▓▓▓▓▒▒▒▒▒▒▒▒▒▓▓▓▓▓▓▓▓▓▓▓▓▓▒▓▒░░▓▓▒▒▒▒▒▒▓▓██████████▓▓█████\n"
		"      ░░░░░░░░░░░░░░░░░░░░░░░░░░░░▒▓▓▓▓▓▓▓▓▓▓▓▓▓▓▓▓▓▓▓▓▓▒▒▓▓▓▓▓▓▓▓▓▓▓▓▒▒▒▒▒▓▒▒░▒▓▓▒▒▒▒▒▒▓███████▓███▓████\n"
		"      ░░░░░░░░░░░░░░░░░░░░░░░░░░░░▓▓▓▓▓▓▓▓▓▓▓▓▓▓▓▓▓▓▓▓▓▓░░░░▓▓▓▓▓▓▓▓▒▒▒▒▒▒▒▒▒▒▒▒▓█▓▓▒▒▒▒▒▒▒████████▓█▓▓▓▓\n"
		"      ░░░░░░░░░░░░░░░░░░░░░░░░░░░▓▓▓▓▓▓▓▓▓▓▓▓▓▓▓▓▓▓▓▓▓▓░░░░░░░░░░▓▓▓▒▒▒▒▒▒▒▒▒▒░▓▓▓▓█▓▒▒▒▒▓▓▒███████▓▓██▓█\n"
		"      ░░░░░░░░░░░░░░░░░░░░░░░░░░▒▓▓▓▓▓▓▓▓▓▓▓████▓▓▓▓▓░░░░░░░░░░░░░░░░▒▓▓▓▒▒▒▒▒▓▓▓▓▒▒▒▓▓▓▓▓▓▒█▓▓▓▓▓▓▓▓▓█▓▓\n"
		"      ░░░░░░░░░░░░░░░░░░░░░░░░░▒▓▓▓▓▓▓▓████████▓▓█▓▓▓▓▓░░░░░░░░░░░░░░░░░░░░░░░░▒▓▓▓▓▓▓▓▓▓▓██▓▓█████▓▓▓▓▓▓\n"
		"      ░░░░░░░░░░░░░░░░░░░░░░░░░▓▓███▓███████████▓▓▓▓▓▓▒░░░░░░░░░░░░░░░░░░░░░░░░▓▓▓▓▓▓▓▒▓██▓██████████▓▓█▓\n"
		"      ░░░░░░░░░░░░░░░░░░░░░░░░▓██▓▓▓▓▓▓▓▓▓▓████████▓░░░░░░░░░░░░░░░░░░░░░░░░░░░░░▓▓▓▓██▓███████▓███▓█▓▓▓▓\n"
		"      ░░░░░░░░░░░░░░░░░░░░░░░▓▓██████▓▓██████████░░░░░░░░░░░░░░░░░░░░░░░░░░░░░░░░▓▓▓▓▓███████▓██████▓▓███\n"
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
	"                                    ░░░░░░▒▒▓▓█████████▓▓▒▒░░░░░░                                    \n"
	"                                    ░░░░░░░░░░░░░░░░░░░░░░░░░░░░░                                    \n"
	"\n");
}

void console_gfx_welcome_msg(){
	util_print_nice("          AND!XOR DC26 BADGE            \n");
	util_print_nice("                                        \n");
	util_print_nice("   @andnxor @zappbrandnxor @hyr0n1      \n");
	util_print_nice("   @exc3ls1or @lacosteaef @bitstr3m     \n");
	util_print_nice("                                        \n");
	util_print_nice("          #BADGELIFE IS PAIN            \n");
	util_print_nice("                                        \n");
	util_print_nice("    M~~.          I~~M                  \n");
	util_print_nice("    .~~.       .=~~~~~~~.       .~~     \n");
	util_print_nice("     ~~.       ~~~~~~~~~~       ~~.     \n");
	util_print_nice("     .~+       ~~~MM~~~~~M     M~=      \n");
	util_print_nice("      ~~      ~DM~~~,8,,~.    M~.       \n");
	util_print_nice("       ~.     ~DD88DDDD~~    Z~.        \n");
	util_print_nice("       .~.     .~MI,.:,~ .Z~~+          \n");
	util_print_nice("         .~~~M...=~~$D~~,.              \n");
	util_print_nice("              .$~~~~.                   \n");
	util_print_nice("               .~~~~                    \n");
	util_print_nice("               +~~~~                    \n");
	util_print_nice("               ~~~~~.                   \n");
	util_print_nice("               ~~~~~~                   \n");
	util_print_nice("              .~~~~~~                   \n");
	util_print_nice("              .~~~~~~?                  \n");
	util_print_nice("              .~~~~~~,                  \n");
	util_print_nice("               N~~~~~                   \n");
	util_print_nice("                ~ .~.                   \n");
	util_print_nice("               ,~  ,,                   \n");
	util_print_nice("               ~I  .~                   \n");
	util_print_nice("              .~.   ~.                  \n");
	util_print_nice("              .~.   =:                  \n");
	util_print_nice("               ~.   :~                  \n");
	util_print_nice("               ,~   ~~                  \n");
	util_print_nice("               .~   ~~                  \n");
	util_print_nice("               .~,  ~~.                 \n");
	util_print_nice("             .N~~~  ~~M.                \n");
	util_print_nice("            =MMM?. ,~~~.              \n\n");
}
